BillS13iv/HynConn/Male and Female Connector Images.pdf

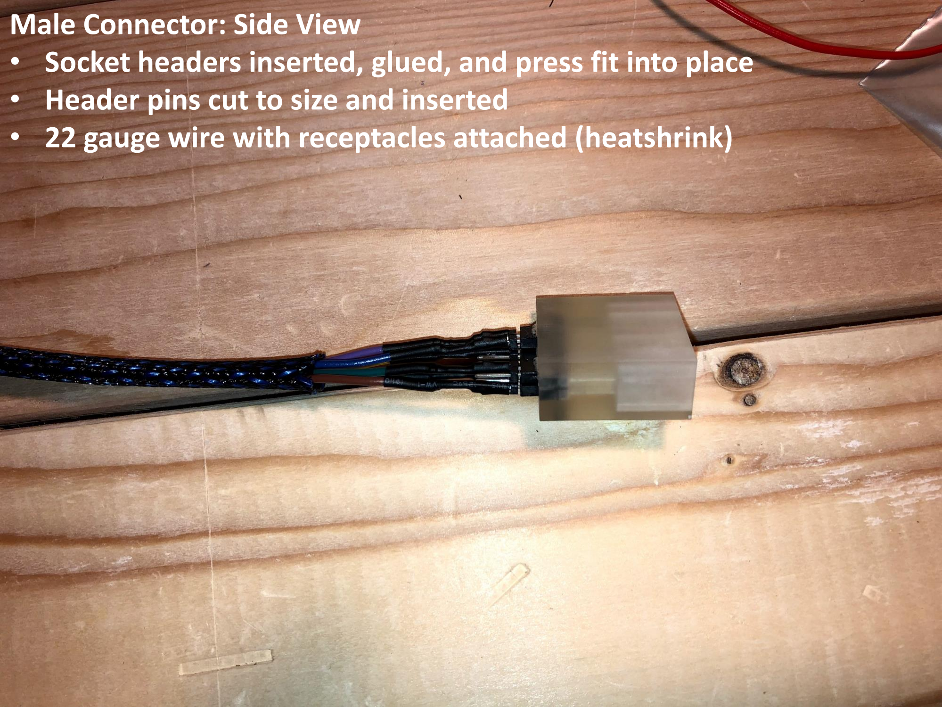
[picture p1: page 1]

Male Connector: Side View
- Socket headers inserted, glued, and press fit into place
- Header pins cut to size and inserted
- 22 gauge wire with receptacles attached (heatshrink)

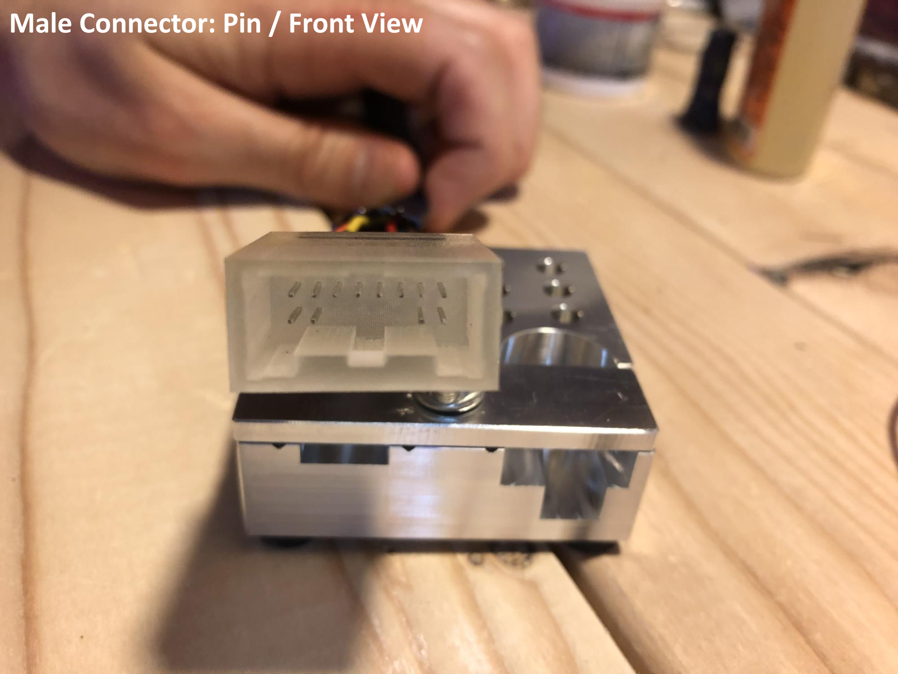
[picture p2: page 2]

Male Connector: Pin / Front View

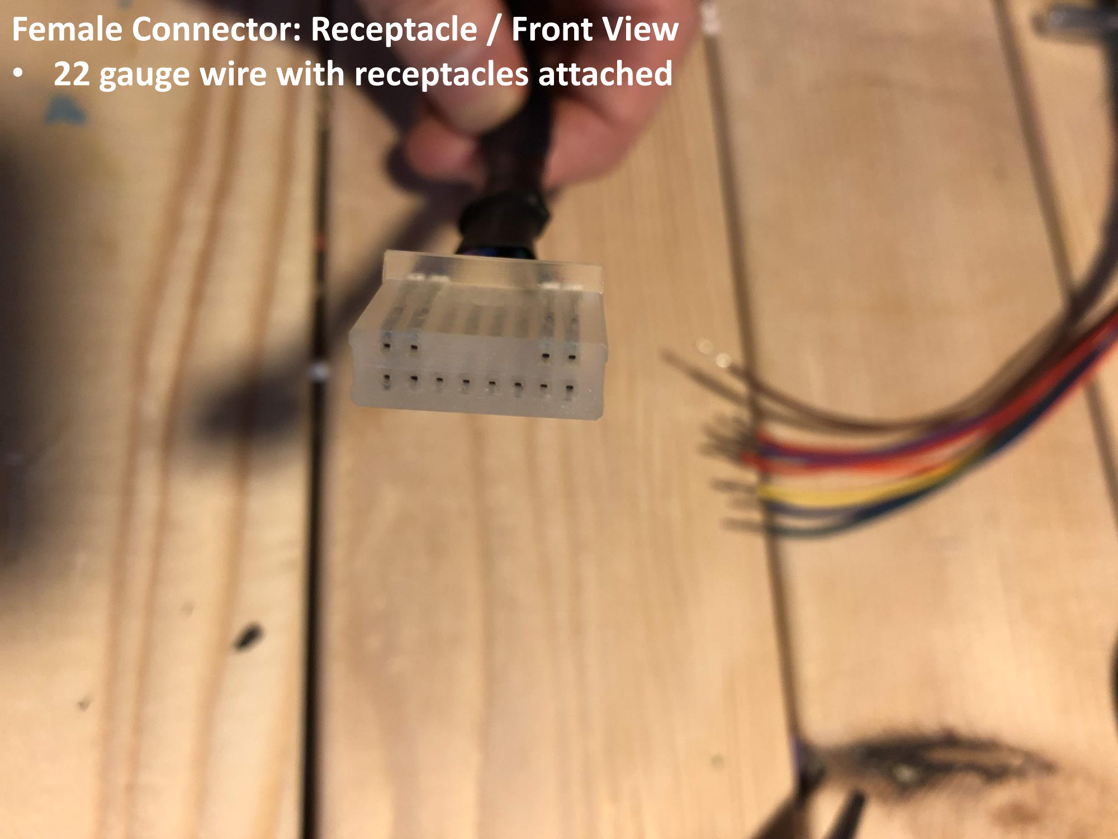
[picture p3: page 3]

Female Connector: Receptacle / Front View
- 22 gauge wire with receptacles attached

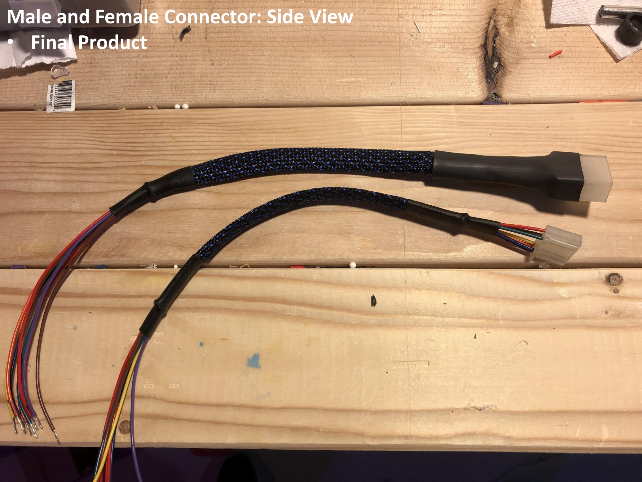
[picture p4: page 4]

Male and Female Connector: Side View
- Final Product
