BillS13iv/HynConn/Hyn Connectors - BOM - 4.29.19.pdf

3D Printed Connector: | | Notes:
Supplier: | Shapeways
Material: | Smoothest Fine Detail Plastic (Acrylic) | https://www.shapeways.com/materials/fine-detail-plastic
Female Connector: | $10.50
Male Connector: | $10.68
Shipping: | $4.99
Tax (NY): | $2.29
Total (For 1 Male and 1 Female): | $28.46
Total (For 10 Male and 10 Female): | $235.76 - Or $23.58 for 1 set

Male Connectors:
Supplier: | Samtec
Header 8 pin: | | $0.72 MTMM-108-15-T-S-541
Header 2 pin (Quantity of 2): | | $0.36 MTMM-102-15-T-S-541
Socket 8 pin: | | $1.33 ESQT-102-02-F-S-309
Socket 2 pin (Quantity of 2): | | $1.26 ESQT-108-02-F-S-309
Freight | $1.43
Tax (NY) | $0.45
Total (For 1 Male): | $5.55
Total (For 10 Male): | $41.53 - Or $4.15 for 1 set

Female Connectors:
Supplier: | TE Connectivity / Mouser
Pin Receptacles (Quantity of 20): | | $2.78 2-1703930-1
Freight | $7.99
Tax (NY) | $0.94
Total (For 1 Female): | $11.71
Total (For 10 Female): | $32.61 - Or $3.26 for 1 set

Wire:
Supplier: | McMaster
Black 24 Gauge Space-Saver (10ft): | | $3.00 6450T23
Freight | $8.64
Tax (NY) | $1.02
Total (For 1 Male and 1 Female): | $12.66
Total (For 10 Male and 10 Female): | $42.02 - Or $4.2 for 1 set
Total Pricing (1 set): | $58.38
Total Pricing (5 sets): | $188.50 - Or $37.7 for 1 set
Total Pricing (10 sets): | $351.93 - Or $35.19 for 1 set
