BillS13iv/HynConn/Grey Panda and MDPS - Total Rev2.pdf

# 8P8C to OBD2 – MDPS Version

## IGN

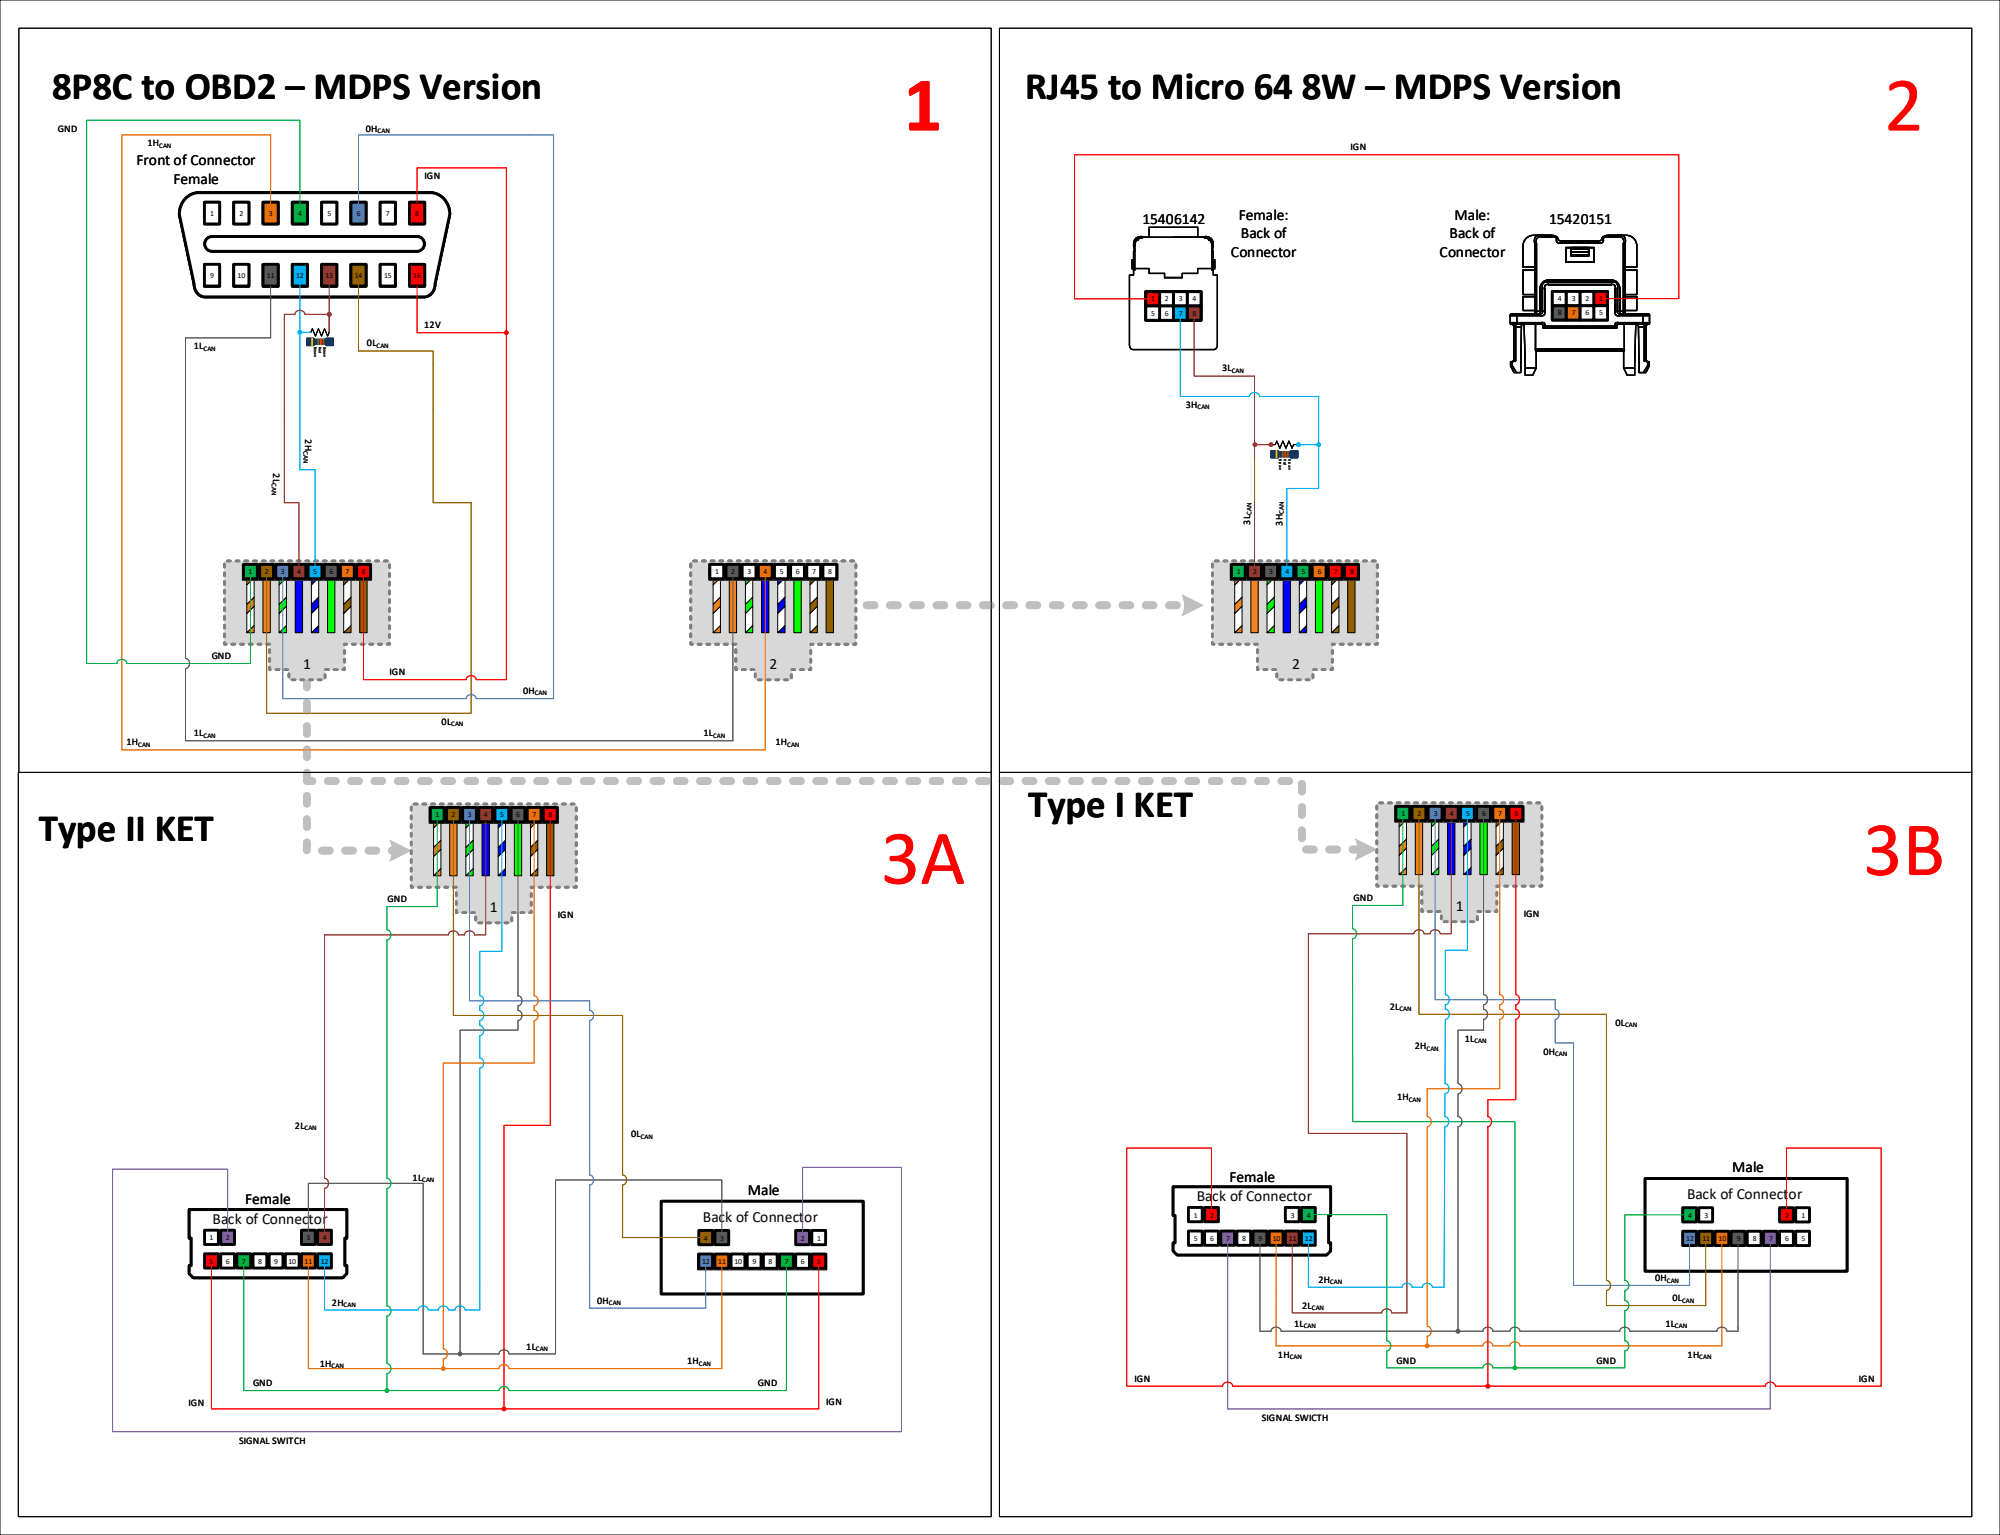
[picture p23: page 1]
8 Brown Red Brown; Front of Connector Female; 1HCAN; 0HCAN; 0LCAN; GND; 2LCAN; 2HCAN; 1LCAN; IGN; 8 ³LCAN; 3HCAN; 3LCAN; Male: Back of Connector; Female: Back of Connector; Female; Male; SIGNAL SWITCH; Type II KET; IGN 1; Type I KET; Back of Connector; SIGNAL SWICTH; 3B Brown Red Brown

8P8C to OBD2 – MDPS Version

RJ45 to Micro 64 8W – MDPS Version

Back of Connector
