BillS13iv/HynConn/MDPS Giraffe with White or Grey Panda.pdf

# 8P8C to OBD2 – MDPS Version

## IGN

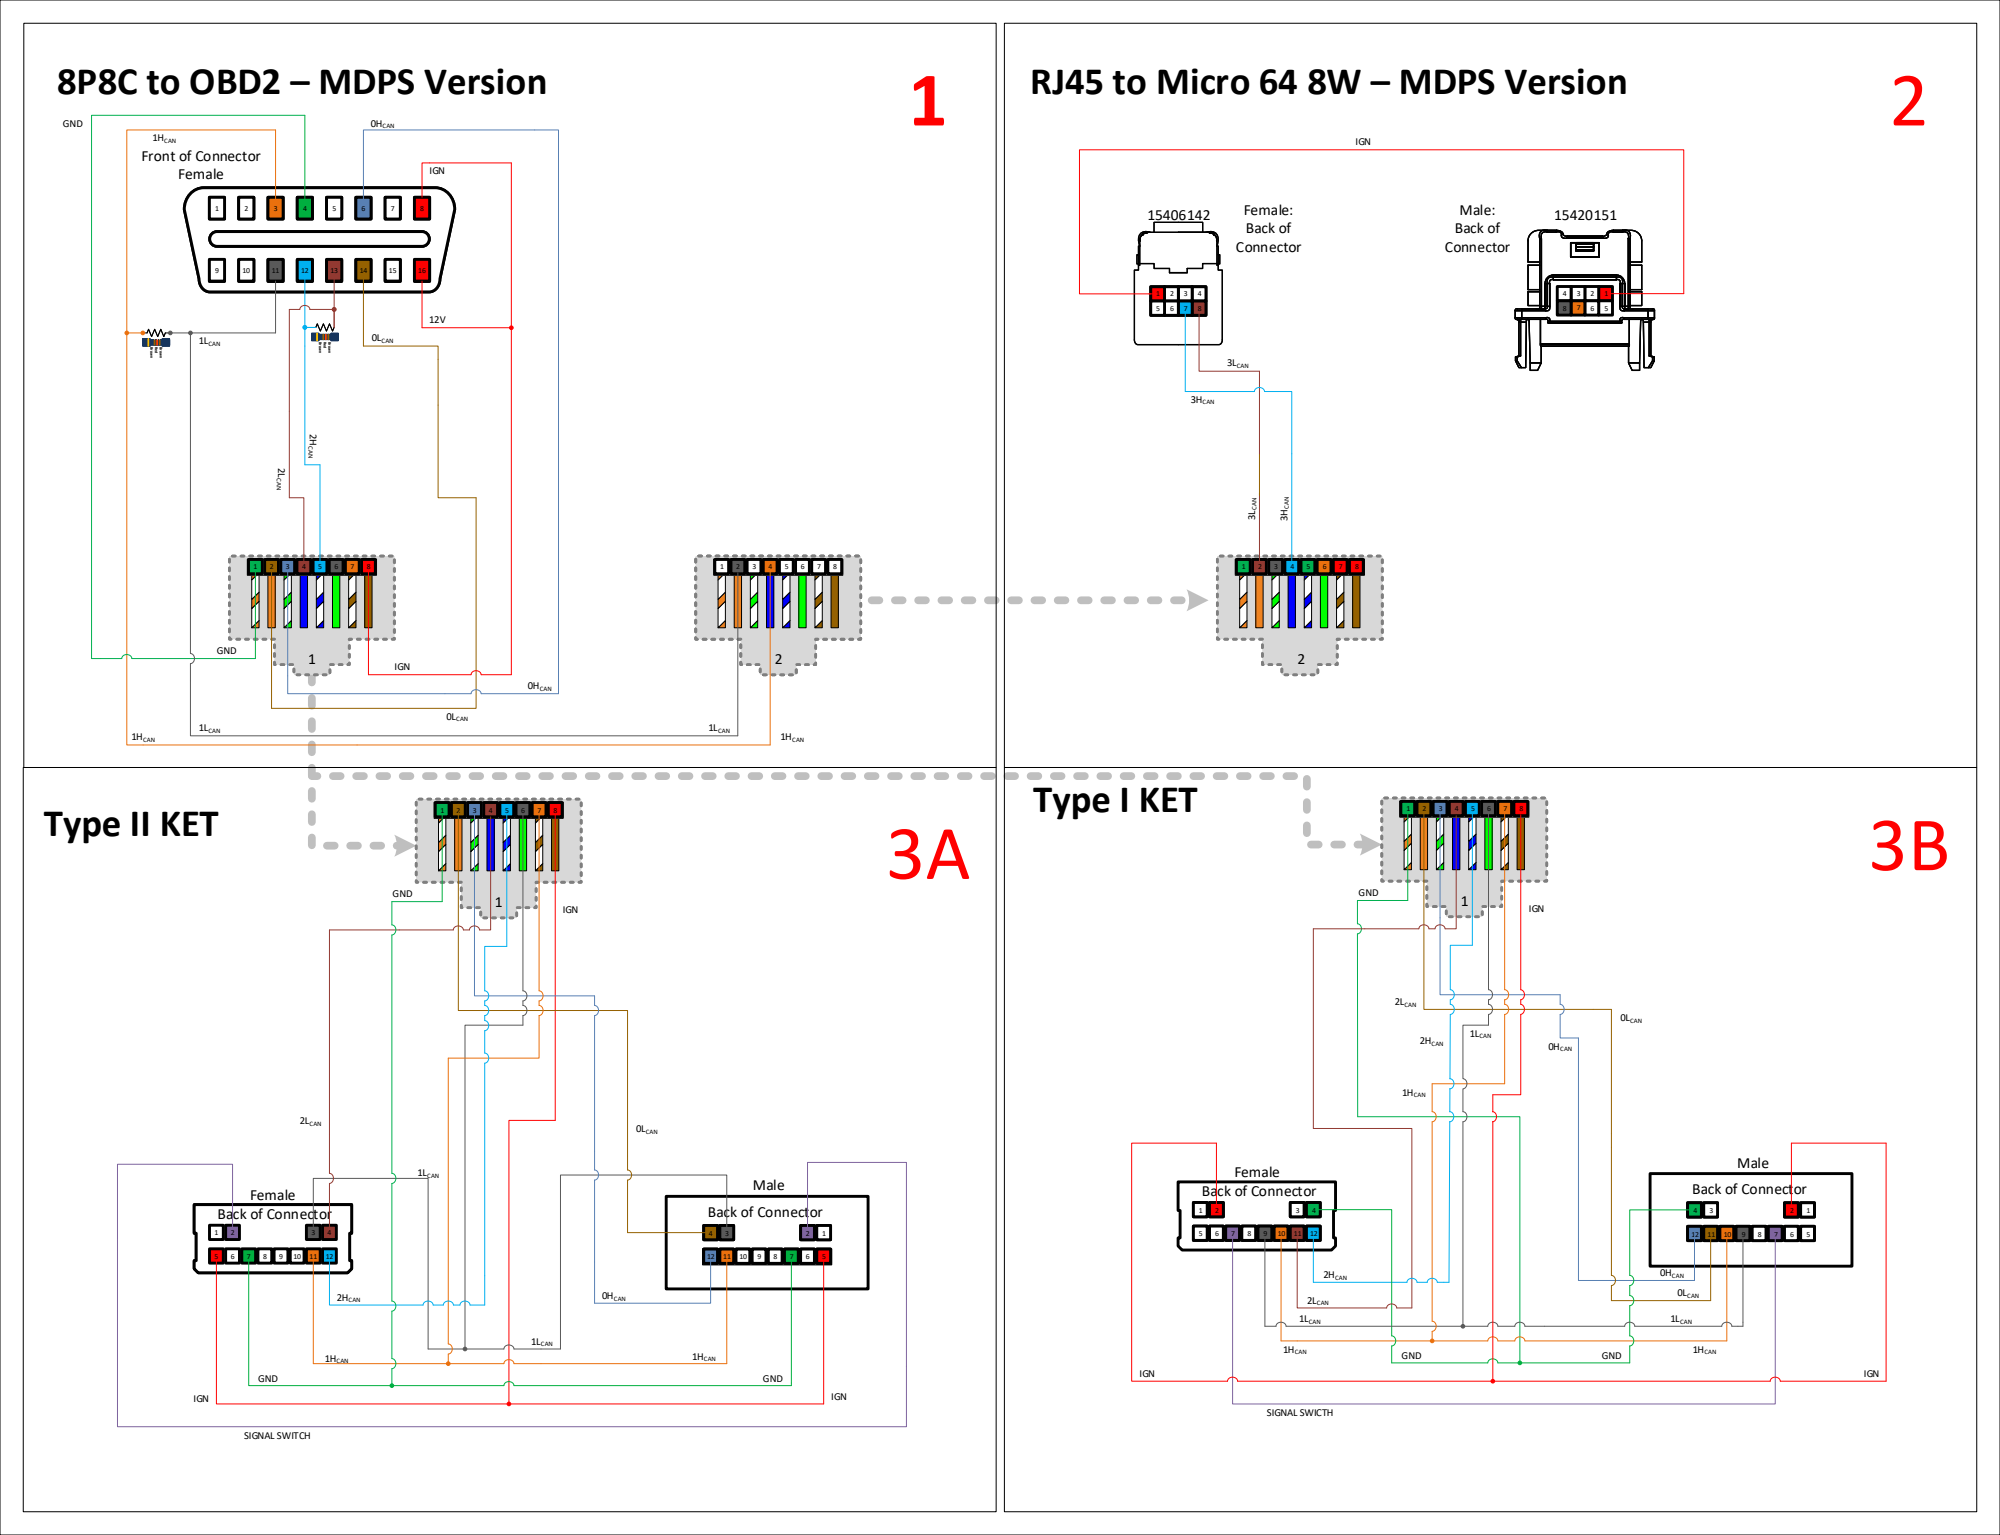
[picture p24: page 1]
8 Br own Red Br own; Front of Connector Female; 1HCAN; 0HCAN; 0LCAN; GND; 2LCAN; 2HCAN; 1LCAN; IGN; Br own; Red; 8 ³LCAN; 3HCAN; 3LCAN; Male: Back of Connector; Female: Back of Connector; Female; Male; SIGNAL SWITCH; Type II KET; IGN 1; Type I KET; Back of Connector; SIGNAL SWICTH

RJ45 to Micro 64 8W – MDPS Version

Back of Connector
